holmesrichards/Mikrokosmos/Images/IMG_6223.JPG

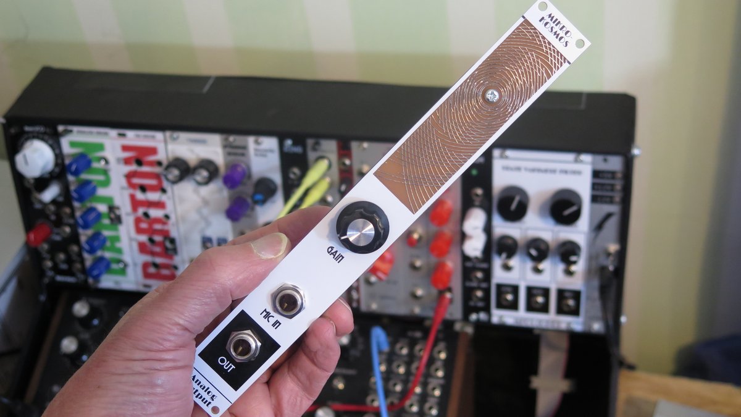
Images/IMG_6223.JPG
