holmesrichards/Mikrokosmos/Images/IMG_6229.JPG

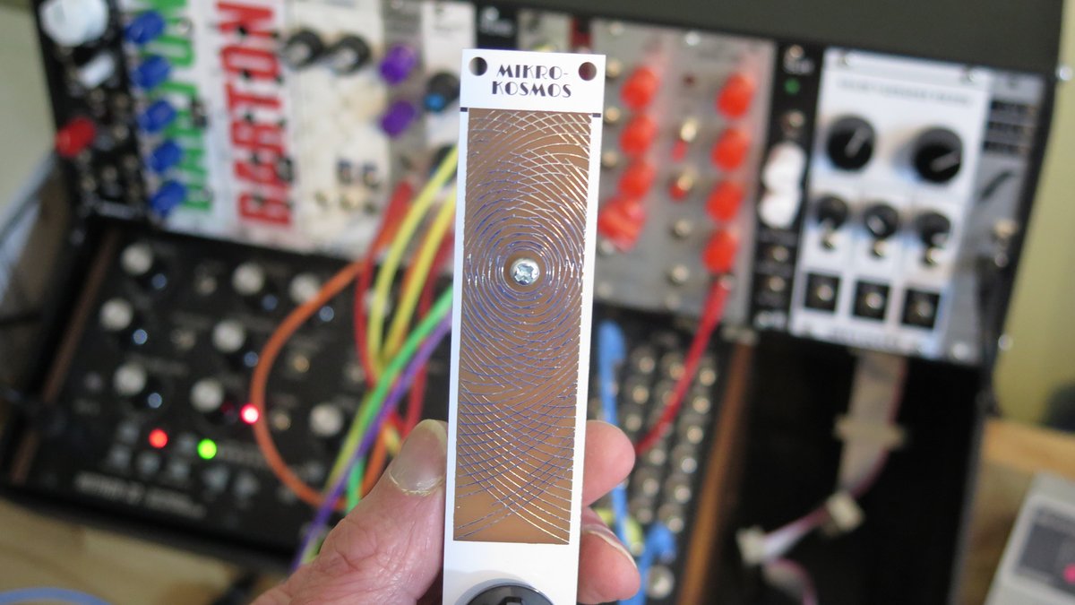
Images/IMG_6229.JPG
